drChungus/Bokkusu/02_Assets/Rails/Eurorack_Rail_Type1.png

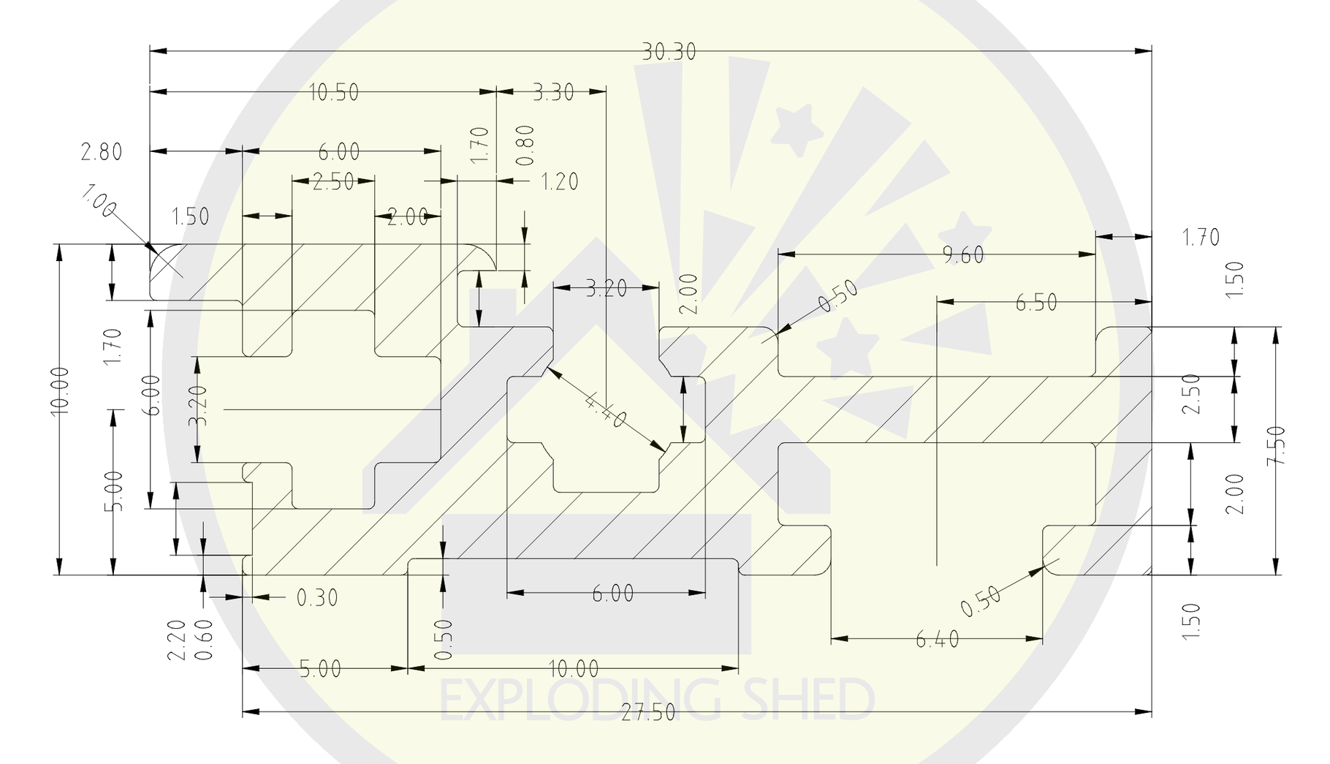
02_Assets/Rails/Eurorack_Rail_Type1.png
