drChungus/Bokkusu/02_Assets/Rails/Eurorack_Rail_Type2.png

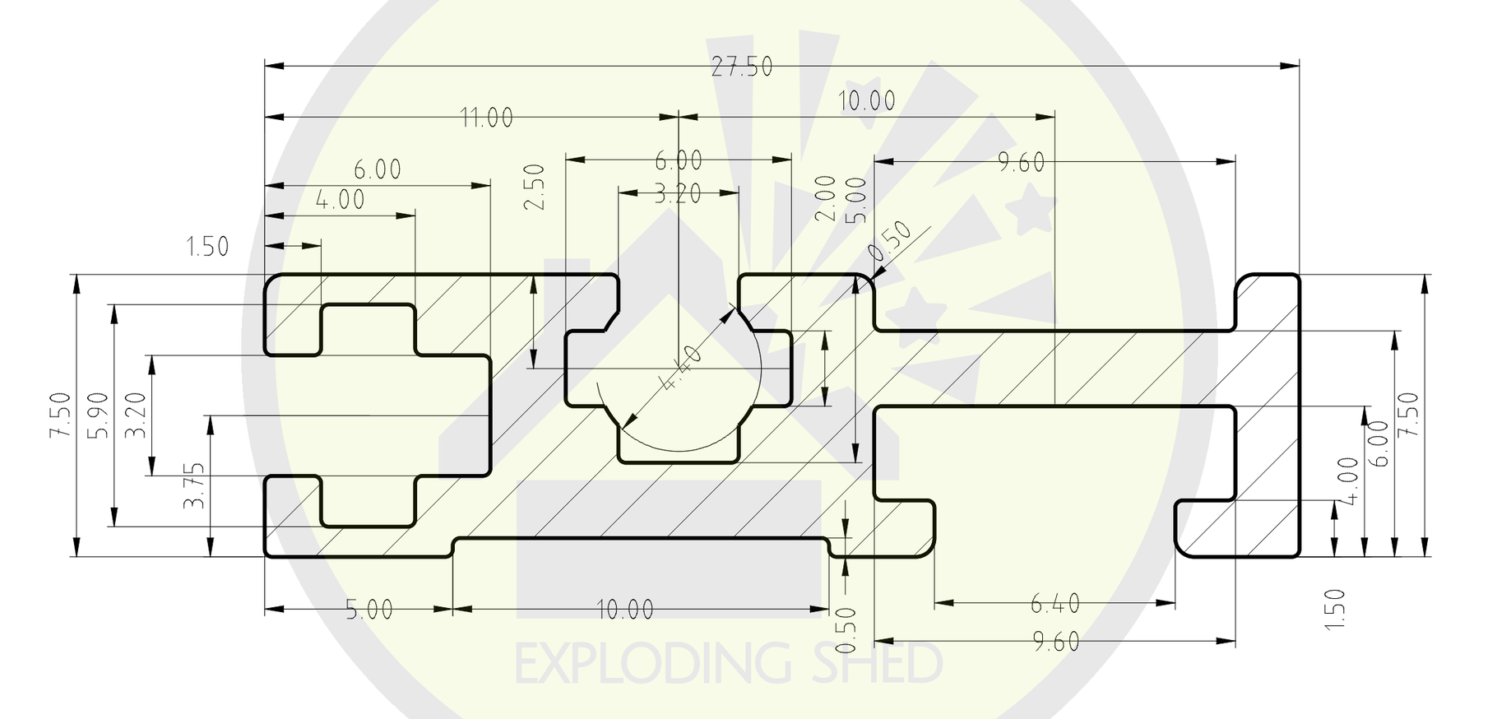
02_Assets/Rails/Eurorack_Rail_Type2.png
