drChungus/Bokkusu/02_Assets/Rails/Rail_TypeA.jpg

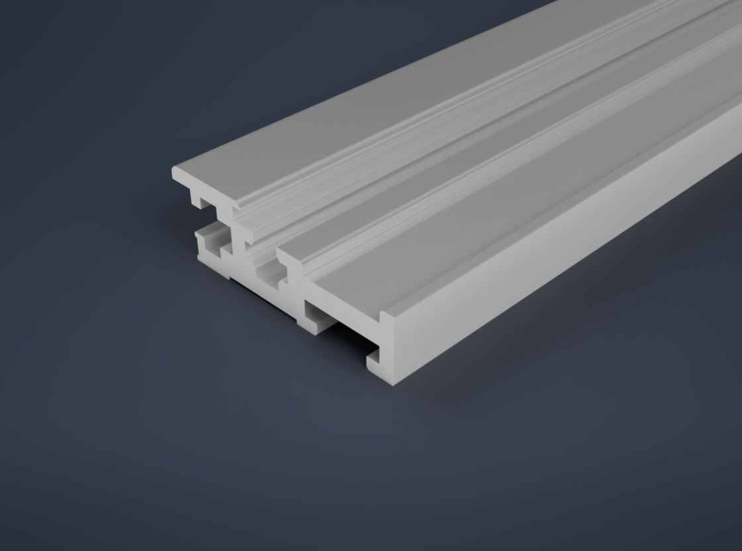
02_Assets/Rails/Rail_TypeA.jpg
