drChungus/Bokkusu/02_Assets/Rails/Rail_TypeB.jpg

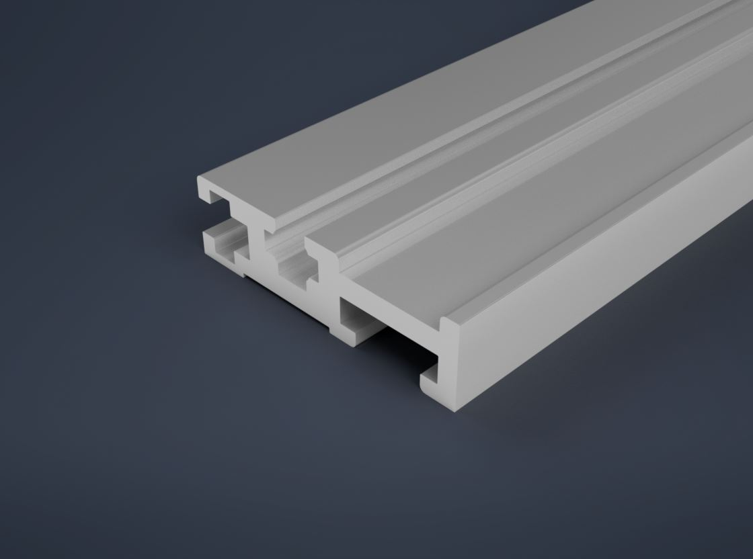
02_Assets/Rails/Rail_TypeB.jpg
