drChungus/Bokkusu/03_Research/1U-vs.-3U-01.png

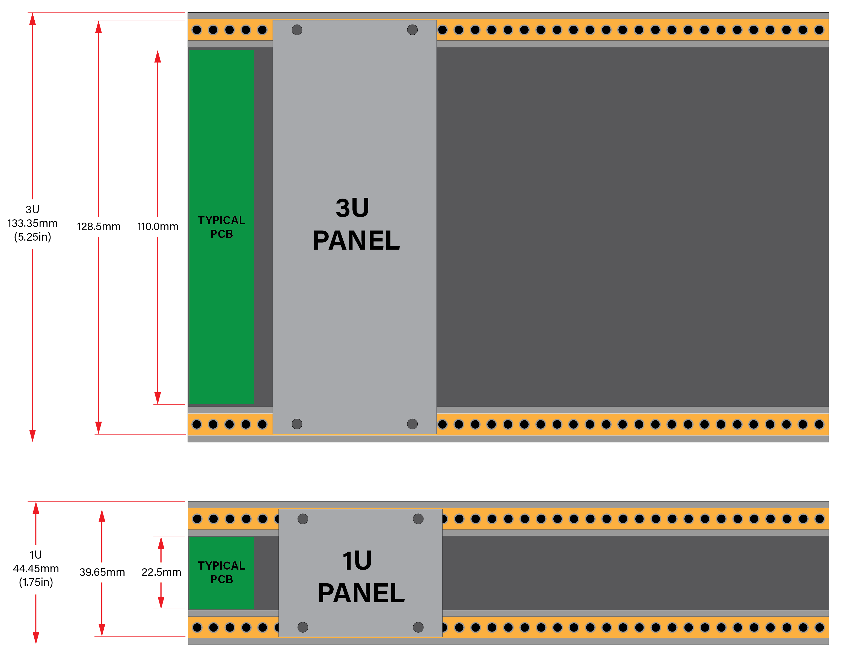
03_Research/1U-vs.-3U-01.png
