drChungus/Bokkusu/07_Production/Images/IMG_20220323_114134.jpg

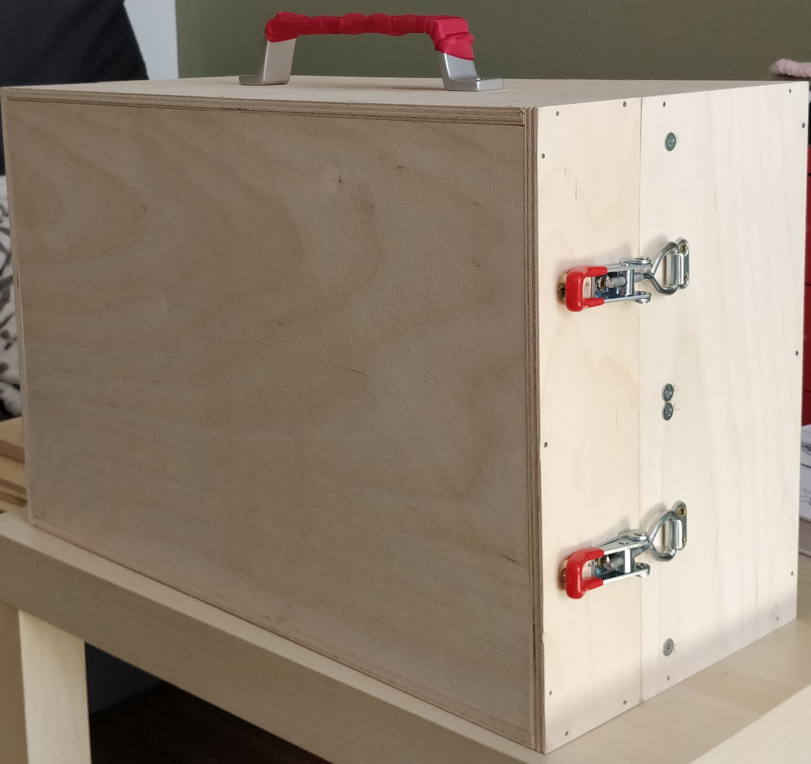
07_Production/Images/IMG_20220323_114134.jpg
