drChungus/Bokkusu/05_Native/Drawings/mainParts.png

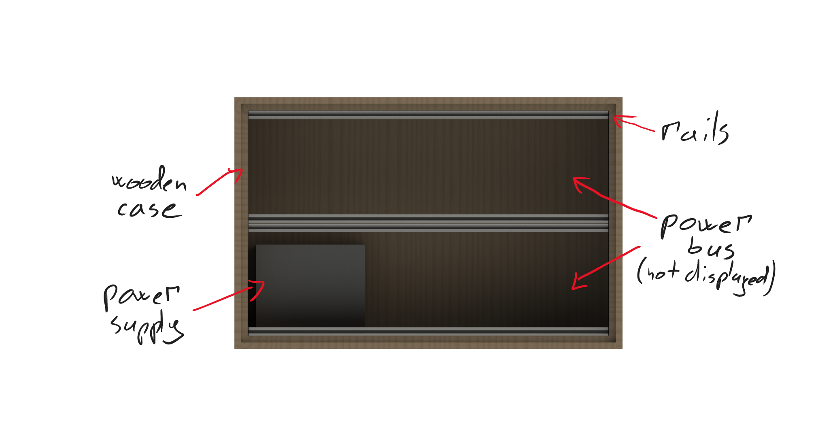
05_Native/Drawings/mainParts.png
